wjlove/WHAQM/documentation/images/carrier-drill.jpg

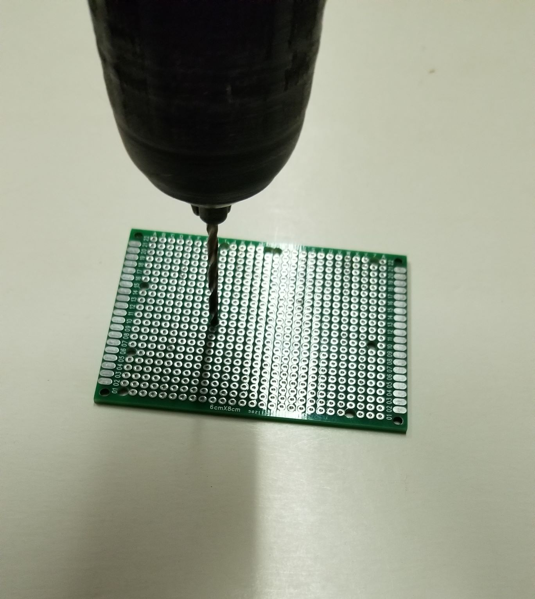
documentation/images/carrier-drill.jpg
