wjlove/WHAQM/documentation/images/case-sizing-holes.jpg

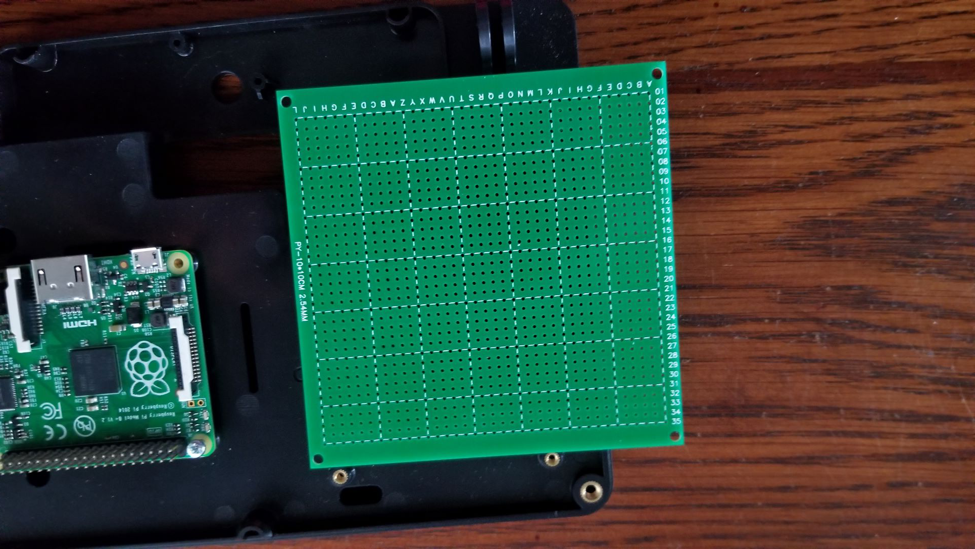
documentation/images/case-sizing-holes.jpg
