wjlove/WHAQM/documentation/images/case-sizing.jpg

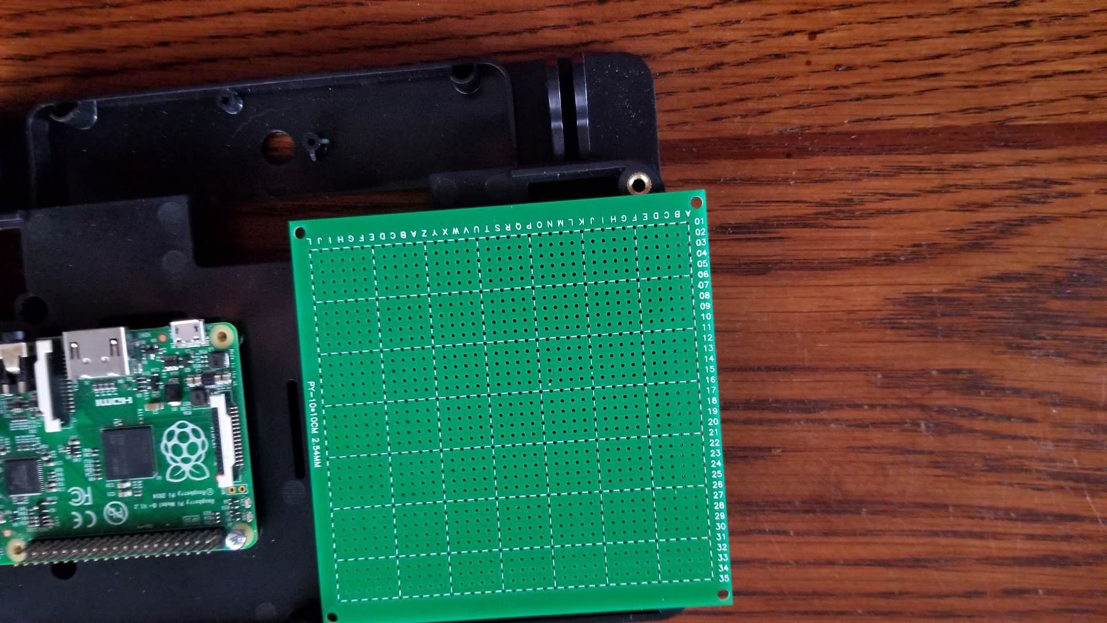
documentation/images/case-sizing.jpg
