wjlove/WHAQM/documentation/images/case-small-fan.jpg

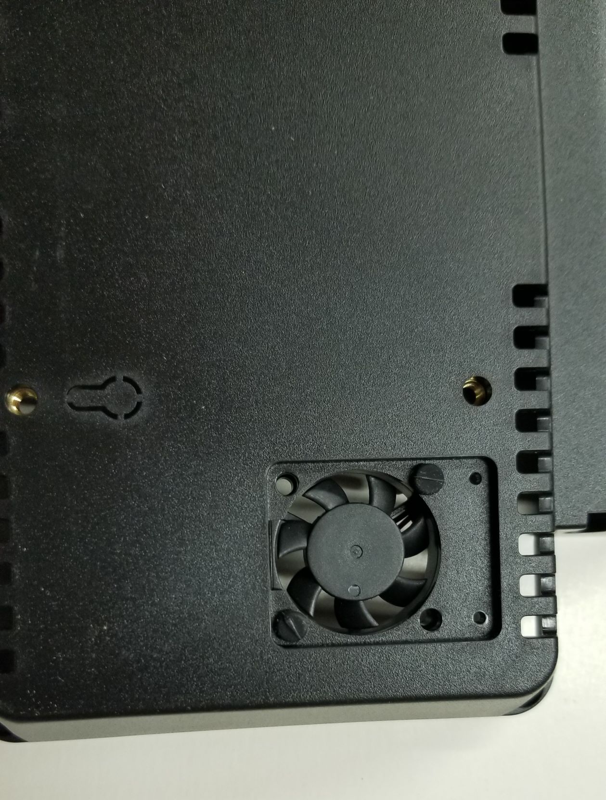
documentation/images/case-small-fan.jpg
