wjlove/WHAQM/documentation/images/cut-cornet-2.jpg

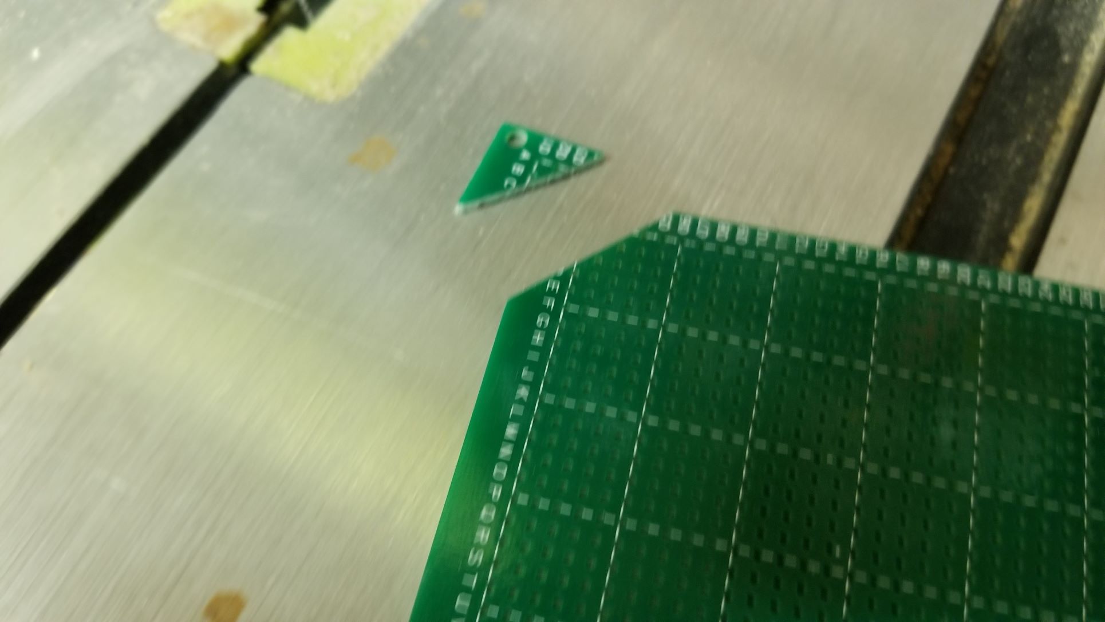
documentation/images/cut-cornet-2.jpg
