wjlove/WHAQM/documentation/images/cut-with-bandsaw-2.jpg

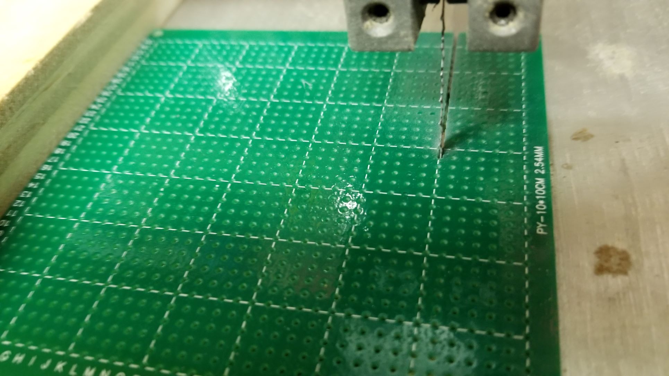
documentation/images/cut-with-bandsaw-2.jpg
