wjlove/WHAQM/documentation/images/empty-case.jpg

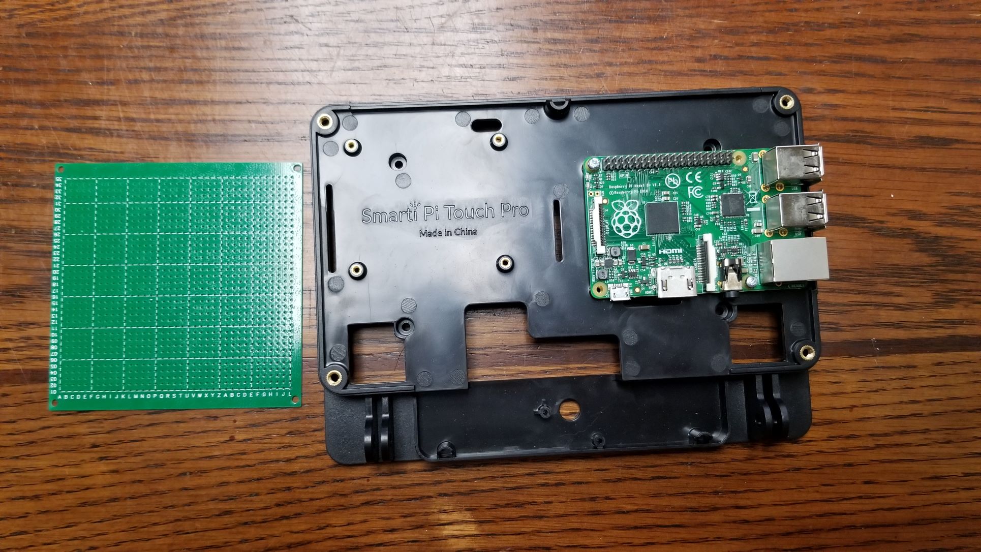
documentation/images/empty-case.jpg
