wjlove/WHAQM/documentation/images/finished-with-stand.jpg

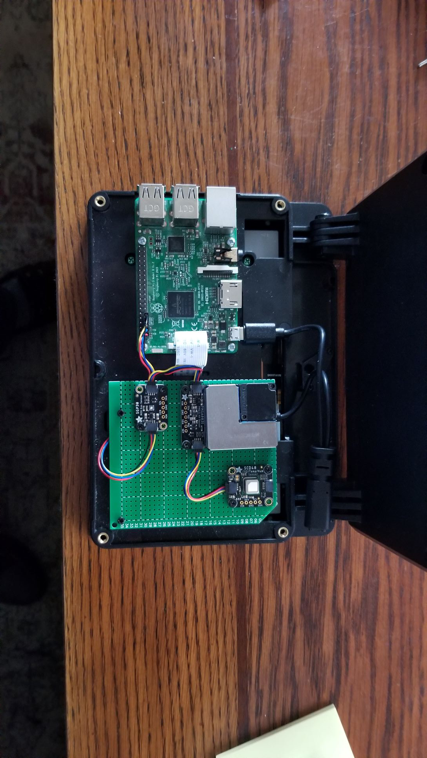
documentation/images/finished-with-stand.jpg
