wjlove/WHAQM/documentation/images/original-pcb-thermo.jpg

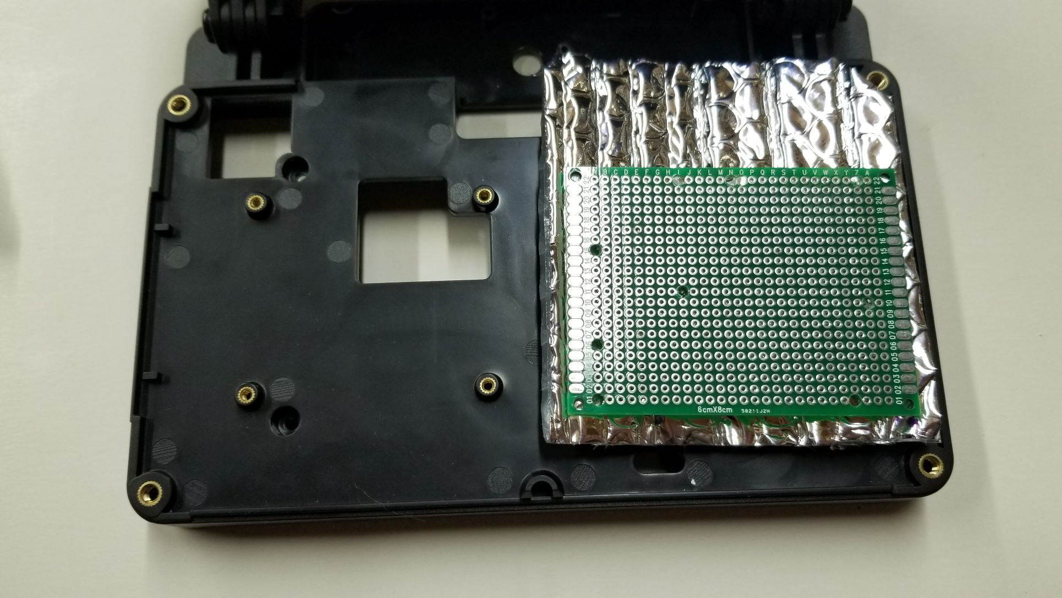
documentation/images/original-pcb-thermo.jpg
