wjlove/WHAQM/documentation/images/pcb-fits-case-with-holes.jpg

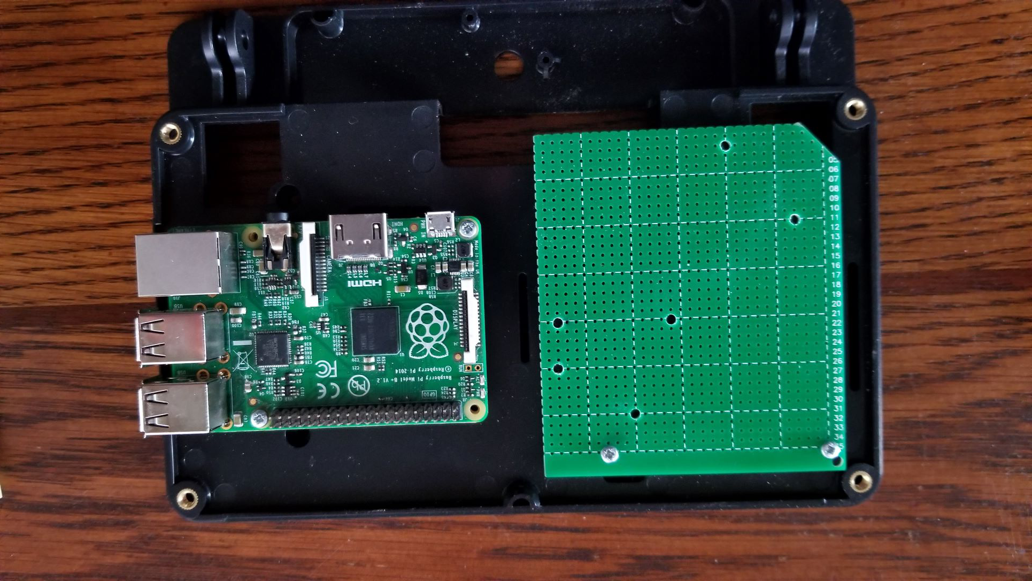
documentation/images/pcb-fits-case-with-holes.jpg
