wjlove/WHAQM/documentation/images/pcb-otpions.jpg

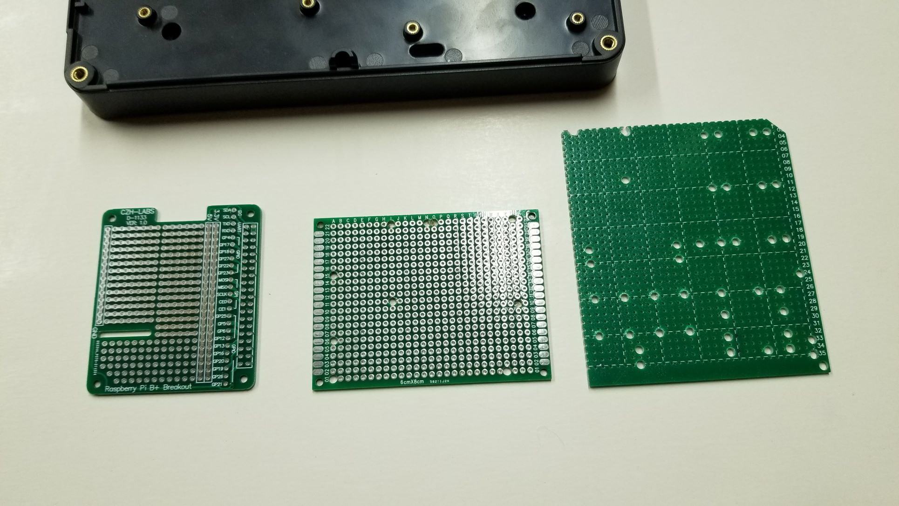
documentation/images/pcb-otpions.jpg
