wjlove/WHAQM/documentation/images/sand-edges.jpg

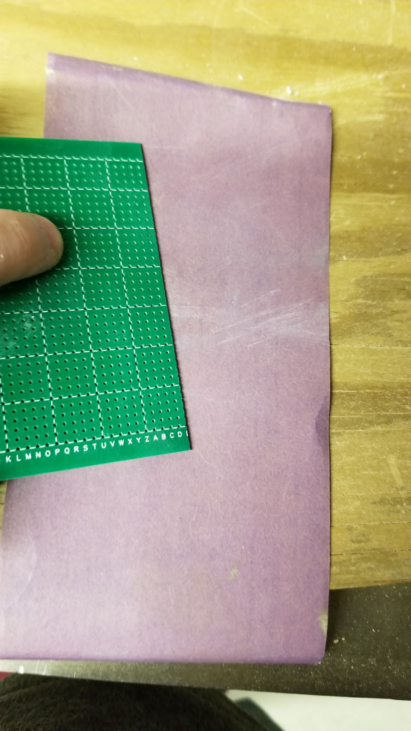
documentation/images/sand-edges.jpg
