wjlove/WHAQM/documentation/images/Screenshot-Deploy-to-fleet.jpg

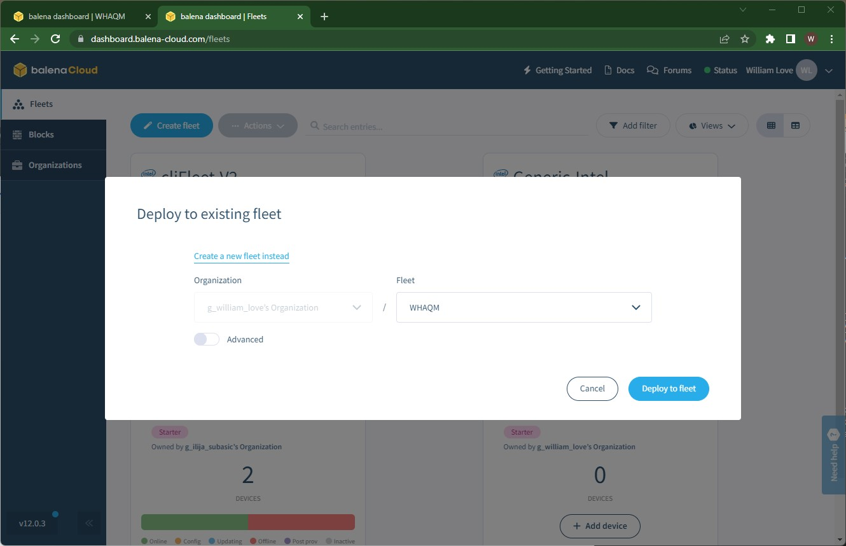
documentation/images/Screenshot-Deploy-to-fleet.jpg
