wjlove/WHAQM/documentation/images/Screenshot-Fleet-no-Devices.jpg

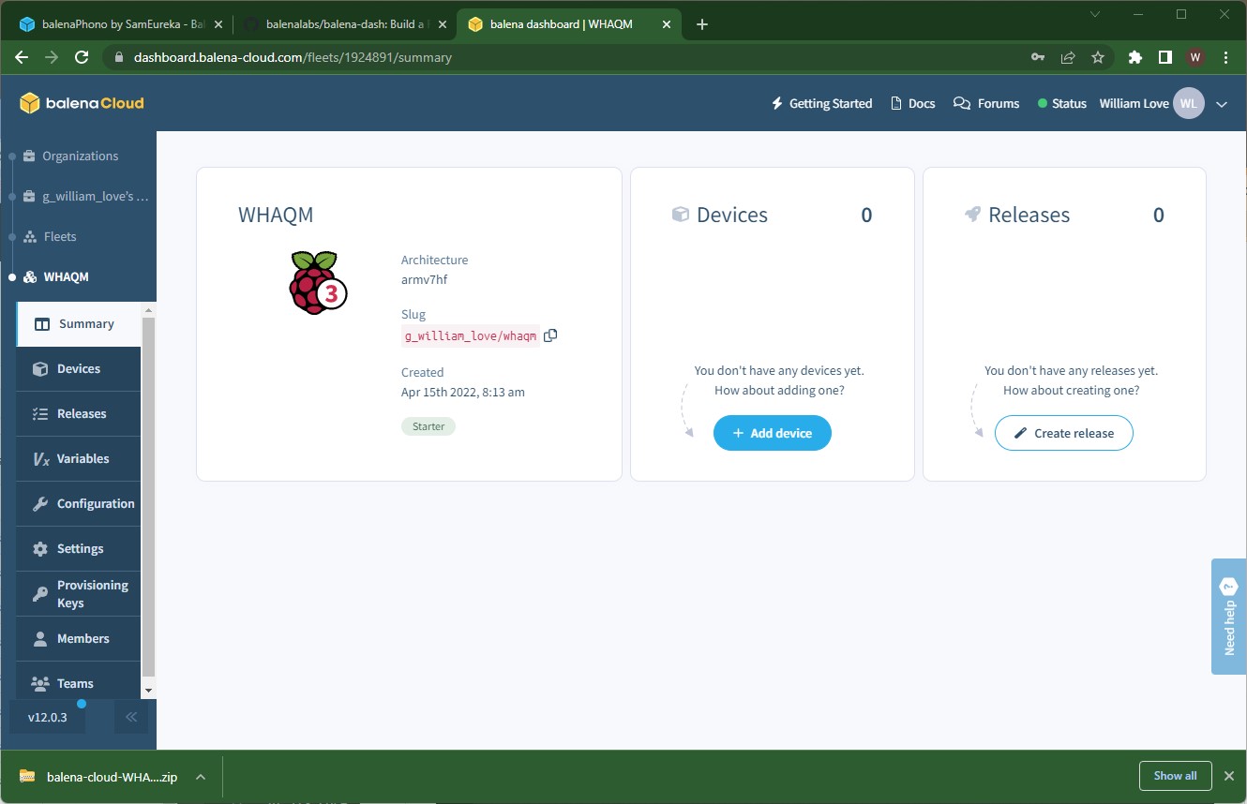
documentation/images/Screenshot-Fleet-no-Devices.jpg
