wjlove/WHAQM/documentation/images/sensors-alone.jpg

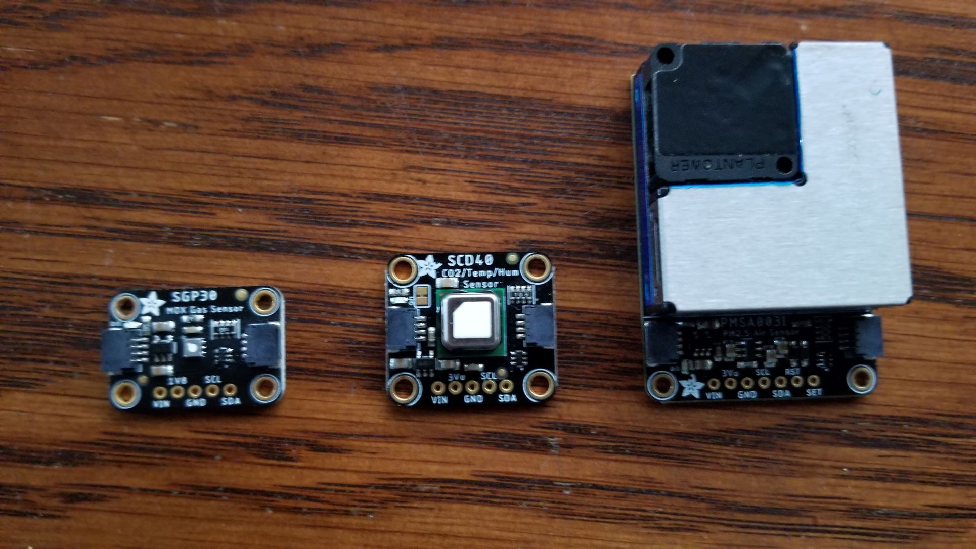
documentation/images/sensors-alone.jpg
