wjlove/WHAQM/documentation/images/single-display-multi-sensors.jpg

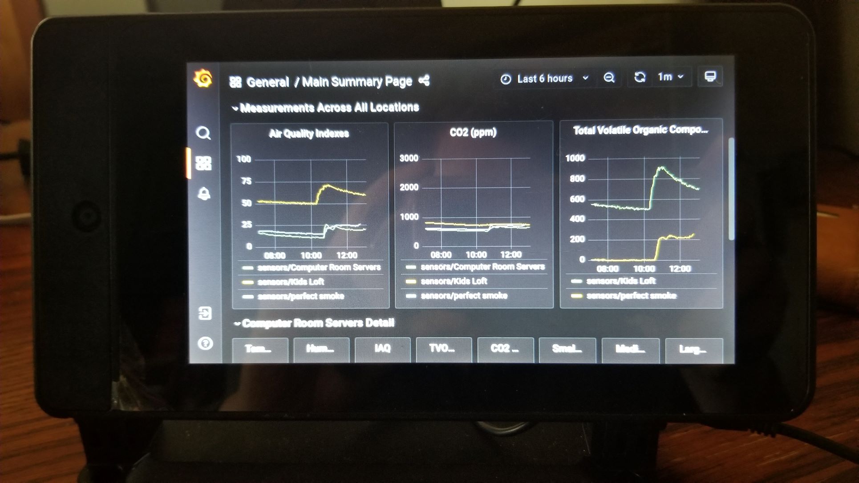
documentation/images/single-display-multi-sensors.jpg
