wjlove/WHAQM/documentation/images/smartipi_open_pi_sensors_on_side.jpg

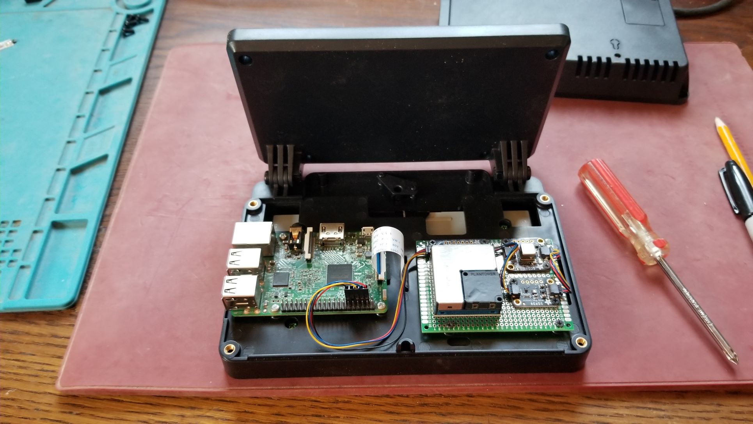
documentation/images/smartipi_open_pi_sensors_on_side.jpg
