wjlove/WHAQM/documentation/images/smartipi_side_complete.jpg

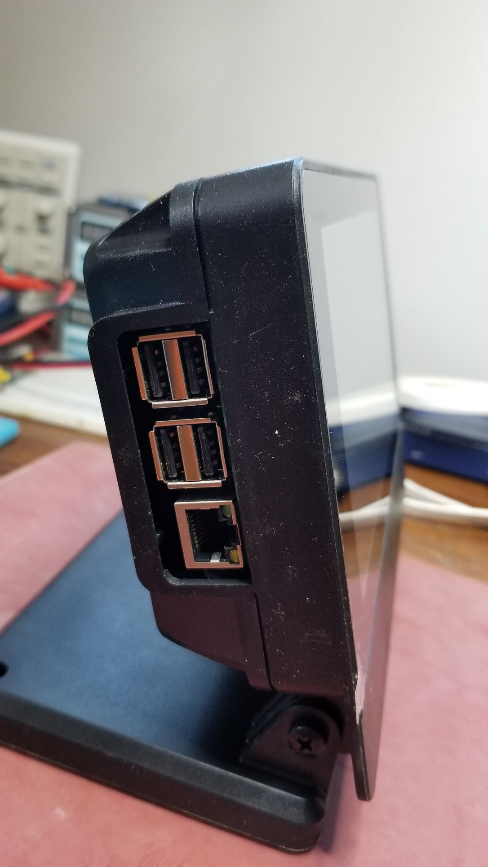
documentation/images/smartipi_side_complete.jpg
