wjlove/WHAQM/documentation/images/smartipi_with_pi_and_screen.jpg

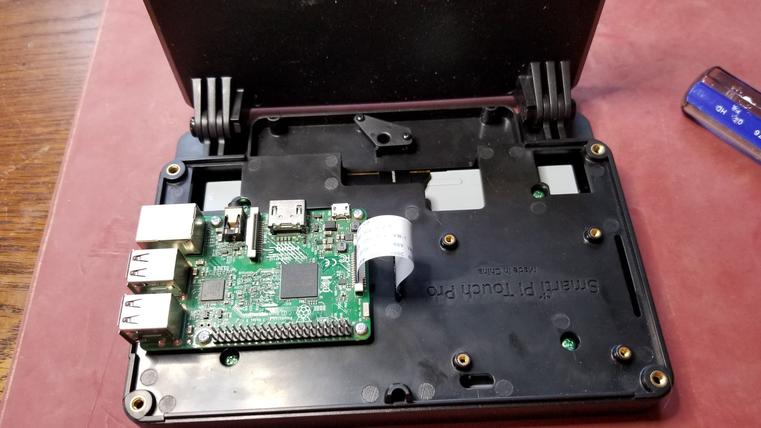
documentation/images/smartipi_with_pi_and_screen.jpg
