wjlove/WHAQM/documentation/images/thermo-options.jpg

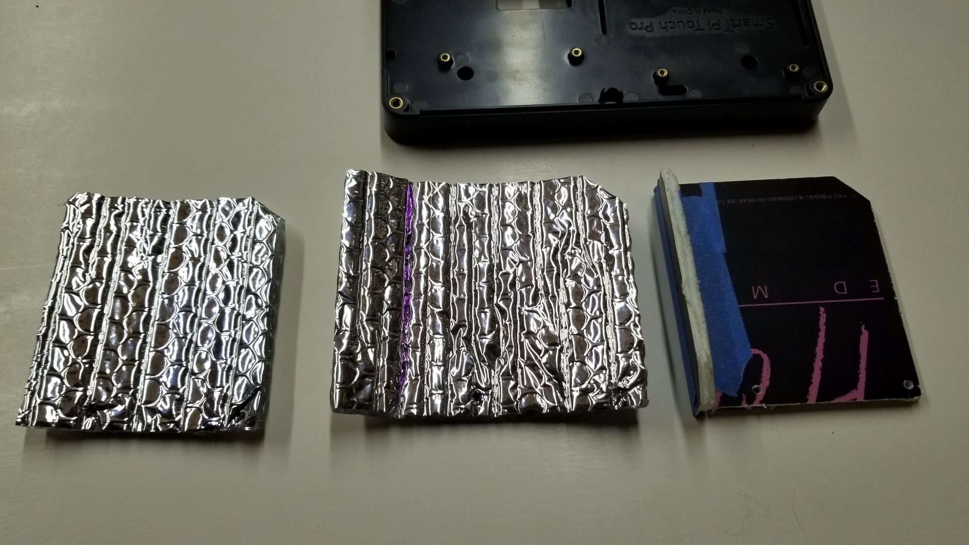
documentation/images/thermo-options.jpg
