wjlove/WHAQM/documentation/images/too-small-pcb.jpg

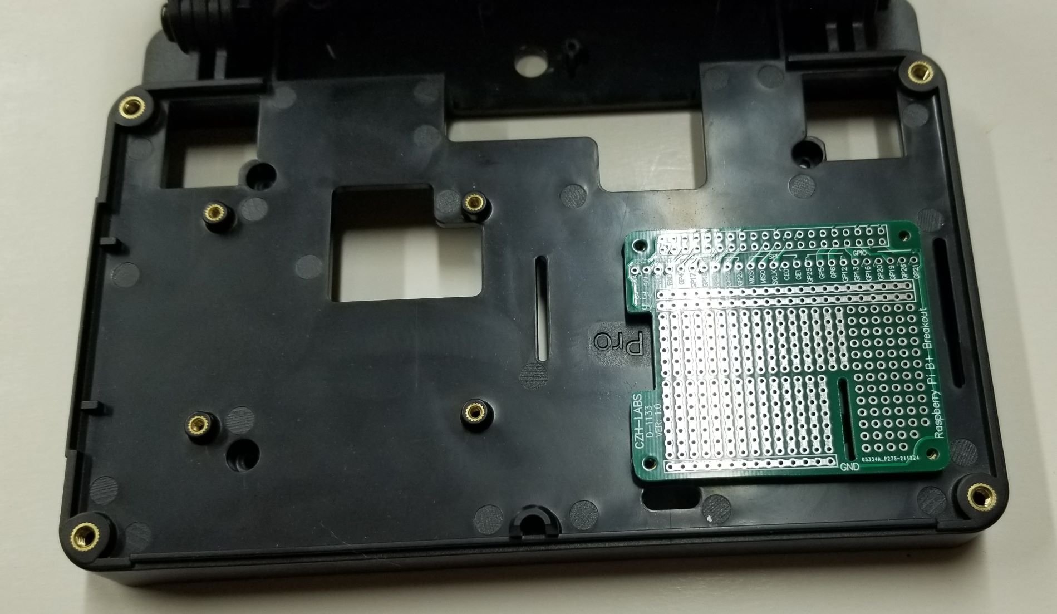
documentation/images/too-small-pcb.jpg
