wjlove/WHAQM/documentation/images/test-holes.jpg

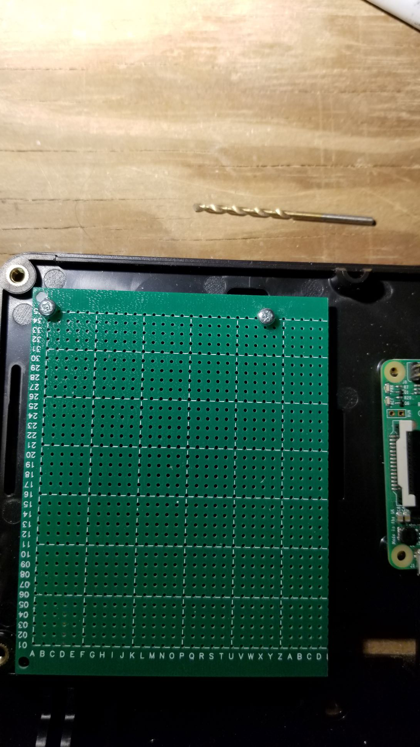
documentation/images/test-holes.jpg
